8bit-Dude/8bit-Hub/Hardware/Parts List/cable_lynx.jpg

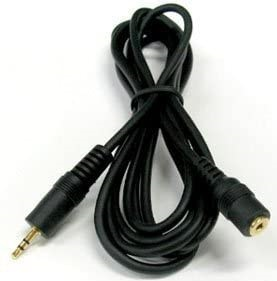
Hardware/Parts List/cable_lynx.jpg
