8bit-Dude/8bit-Hub/Hardware/Parts List/cable_oric.jpg

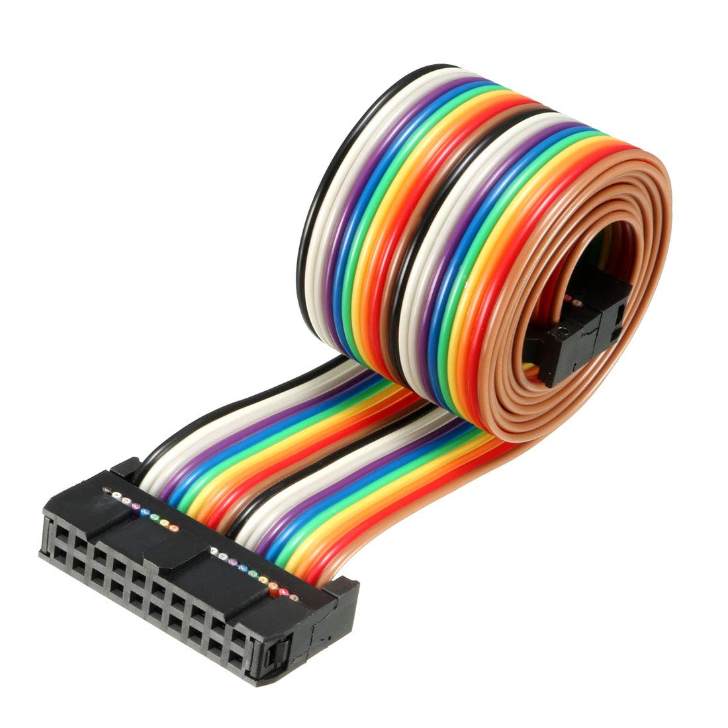
Hardware/Parts List/cable_oric.jpg
