8bit-Dude/8bit-Hub/Hardware/Parts List/db9_shell.jpg

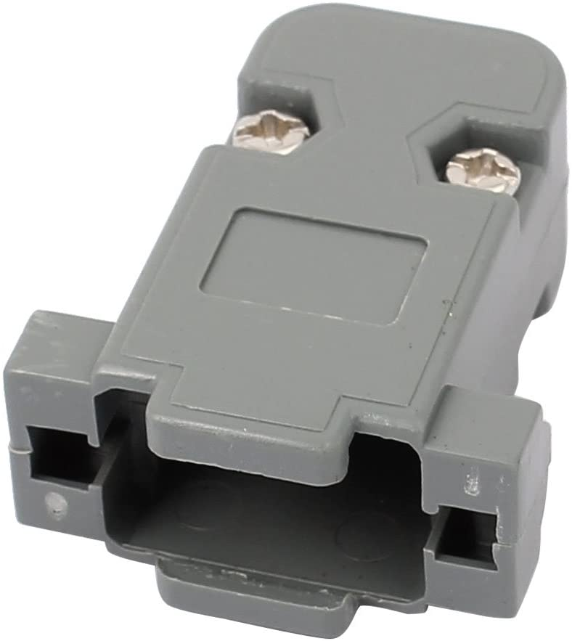
Hardware/Parts List/db9_shell.jpg
