8bit-Dude/8bit-Hub/Hardware/Parts List/lcd.jpg

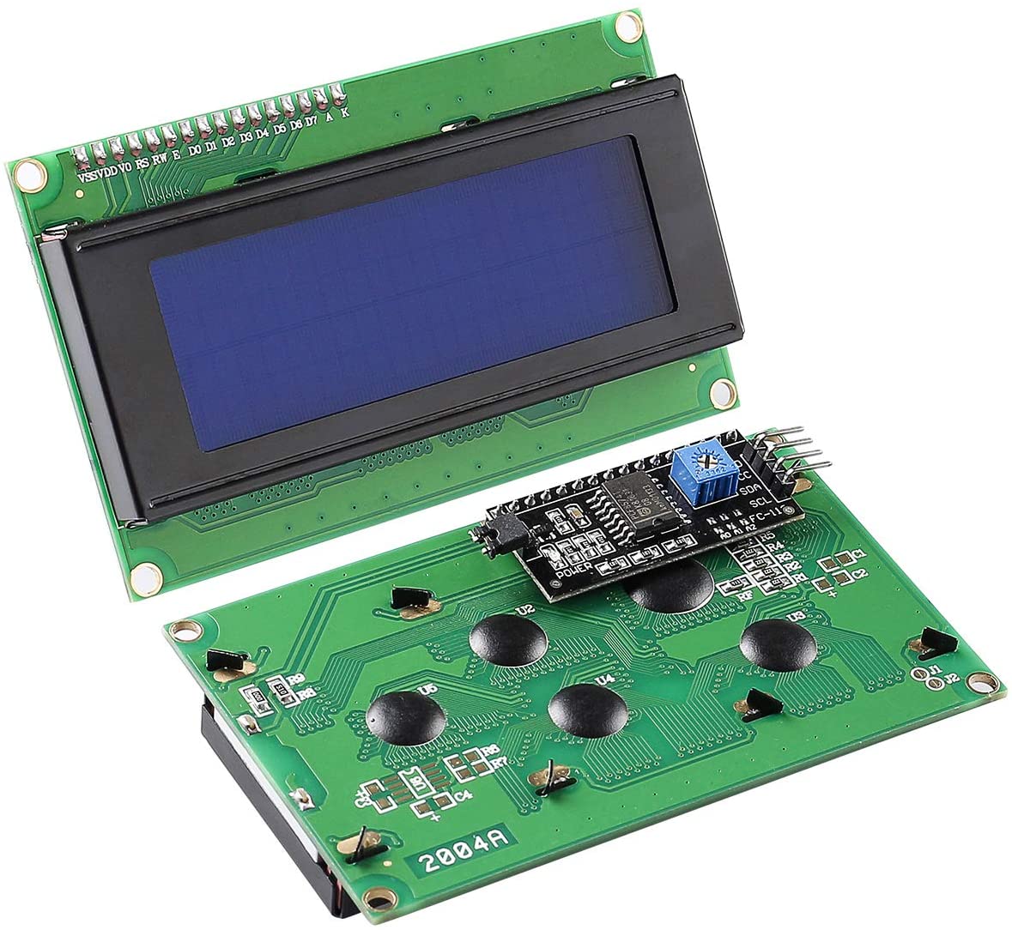
Hardware/Parts List/lcd.jpg
