8bit-Dude/8bit-Hub/Hardware/Parts List/logics_converter.jpg

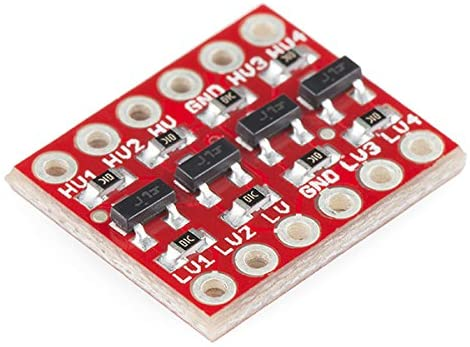
Hardware/Parts List/logics_converter.jpg
