8bit-Dude/8bit-Hub/Hardware/Parts List/microsd.jpg

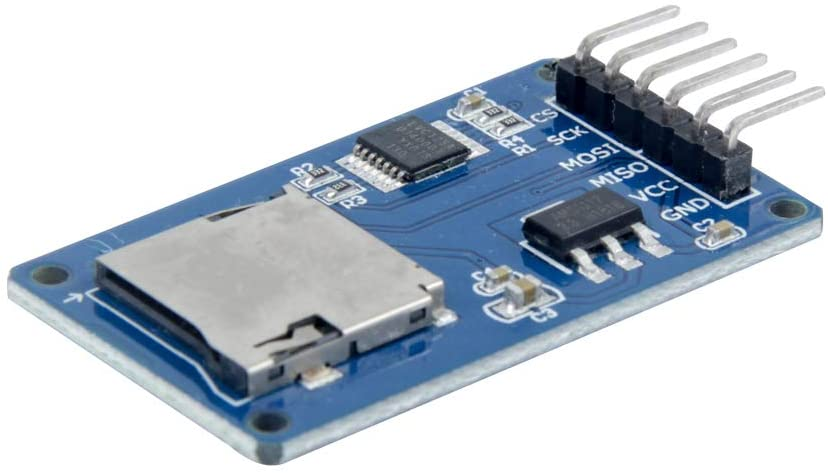
Hardware/Parts List/microsd.jpg
