8bit-Dude/8bit-Hub/Hardware/Parts List/ps2.jpg

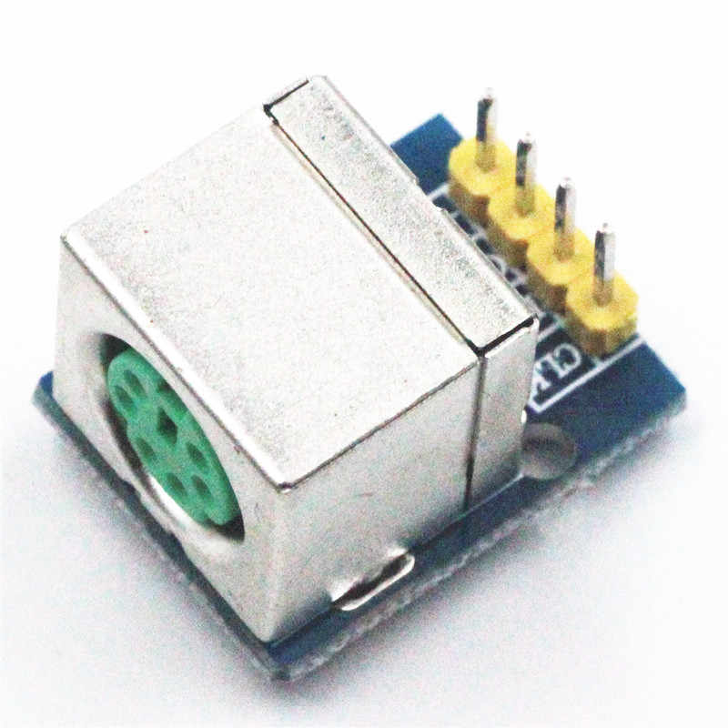
Hardware/Parts List/ps2.jpg
