8bit-Dude/8bit-Hub/Hardware/Parts List/screws.jpg

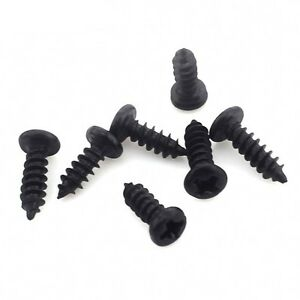
Hardware/Parts List/screws.jpg
