8bit-Dude/8bit-Hub/Hardware/Parts List/3d_printed_case.jpg

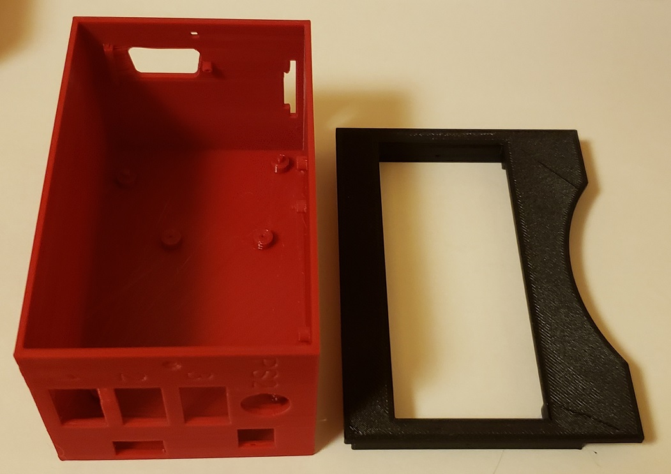
Hardware/Parts List/3d_printed_case.jpg
