8bit-Dude/8bit-Hub/Hardware/Wiring/COM cables.jpg

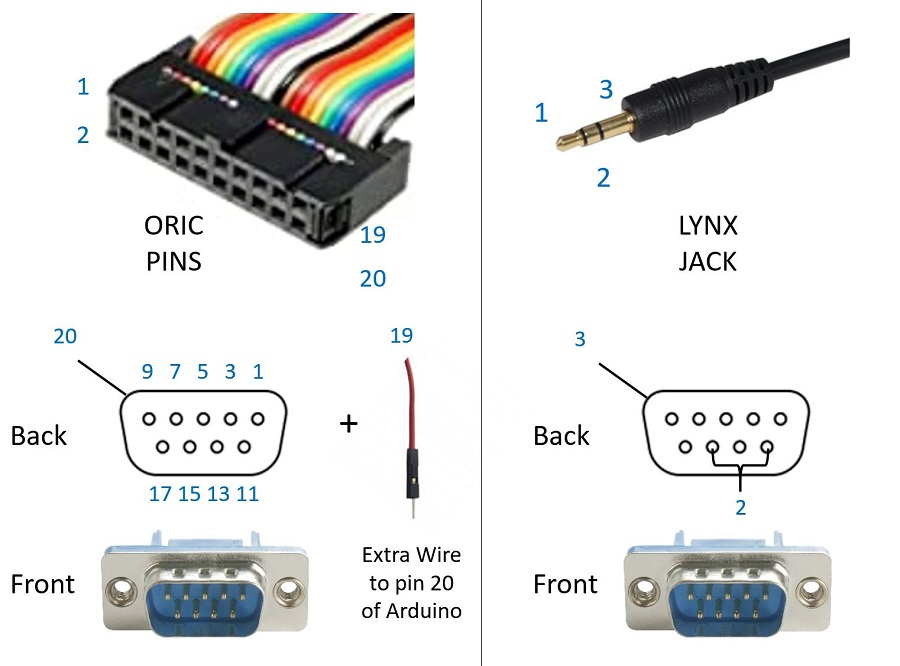
Hardware/Wiring/COM cables.jpg
